MattOr-Creations/SaludWatch/Hardware/kicad/SaludWatch.kicad_sch

## KiCad design Hardware/kicad/SaludWatch.kicad_sch (2026-10-03)

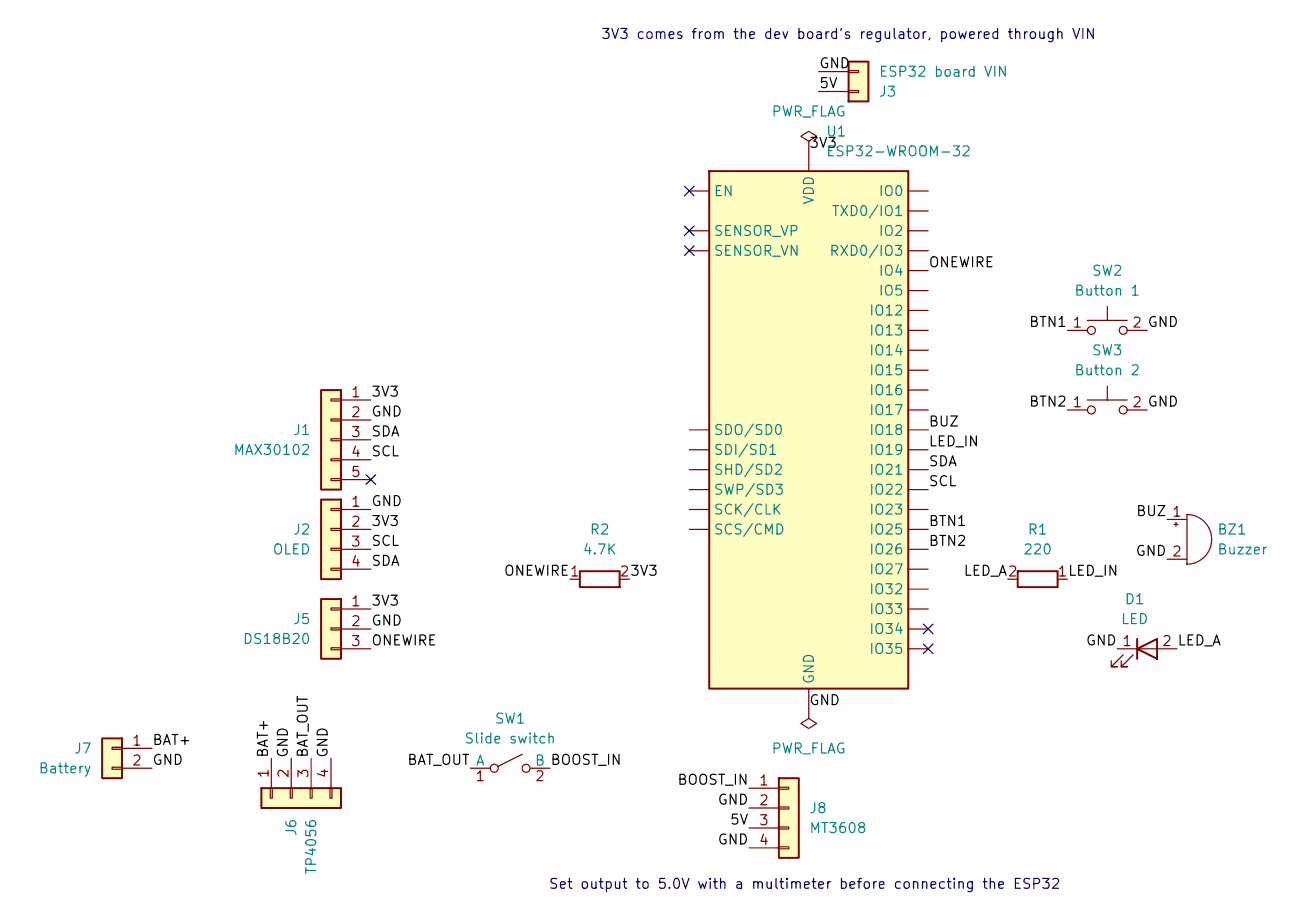
[picture p4: schematic SaludWatch.kicad_sch]

Parts:
BZ1: Buzzer
D1: LED
J1: MAX30102
J2: OLED
J3: ESP32 board VIN
J5: DS18B20
J6: TP4056
J7: Battery
J8: MT3608
R1: 220
R2: 4.7K
SW1: Slide switch
SW2: Button 1
SW3: Button 2
U1: ESP32-WROOM-32

Connections:
3V3: J1.1, J2.2, J5.1, R2.2, U1.2 (VDD)
5V: J3.1, J8.3
BAT+: J6.1, J7.1
BAT_OUT: J6.3, SW1.1 (A)
BOOST_IN: J8.1, SW1.2 (B)
BTN1: SW2.1, U1.10 (IO25)
BTN2: SW3.1, U1.11 (IO26)
BUZ: BZ1.1 (+), U1.30 (IO18)
GND: BZ1.2 (-), D1.1 (K), J1.2, J2.1, J3.2, J5.2, J6.2, J6.4, J7.2, J8.2, J8.4, SW2.2, SW3.2, U1.1 (GND), U1.15 (GND), U1.38 (GND), U1.39 (GND)
LED_A: D1.2 (A), R1.2
LED_IN: R1.1, U1.31 (IO19)
ONEWIRE: J5.3, R2.1, U1.26 (IO4)
SCL: J1.4, J2.3, U1.36 (IO22)
SDA: J1.3, J2.4, U1.33 (IO21)

Notes on the sheet:
3V3 comes from the dev board's regulator, powered through VIN
Set output to 5.0V with a multimeter before connecting the ESP32
